Seba-san/ORR/processing/reportes/perfil_error_temporal_audio_01_10bd.png

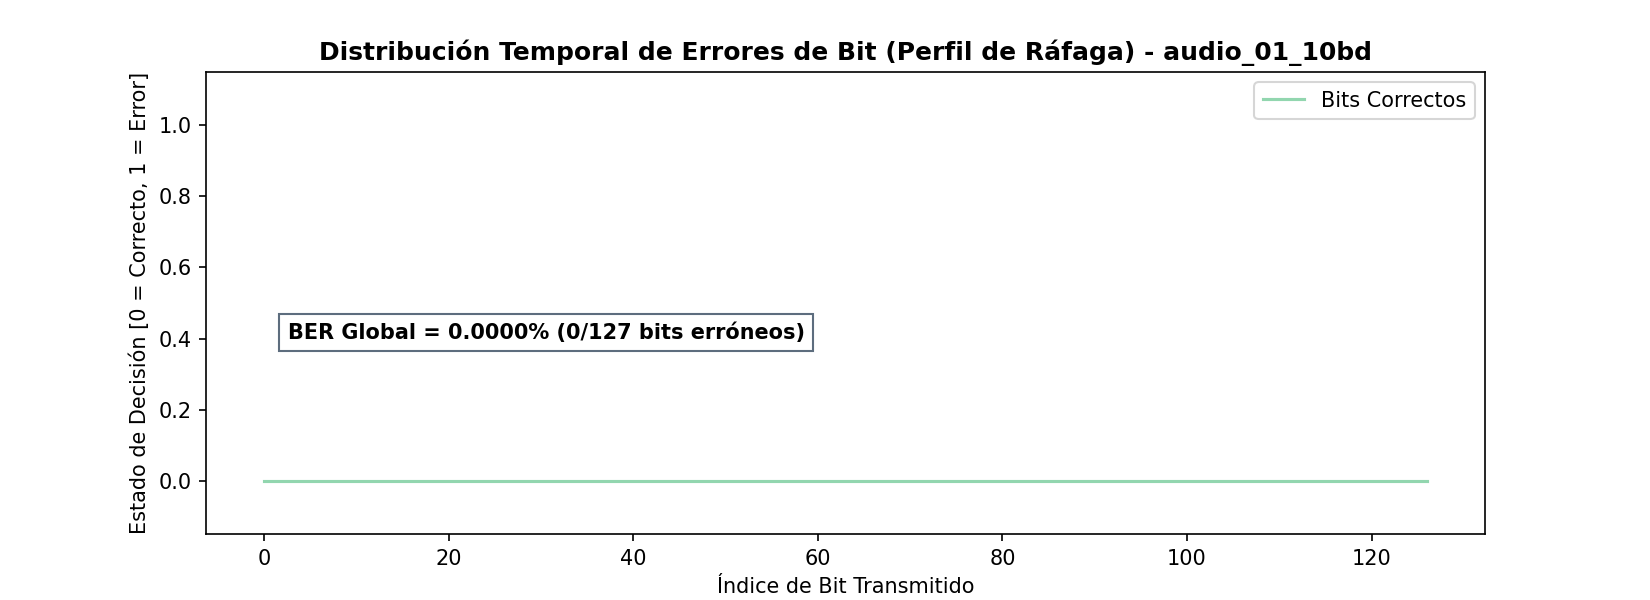
processing/reportes/perfil_error_temporal_audio_01_10bd.png
