Seba-san/ORR/firmware/rx/config.py

# --- CONFIGURACIONES GLOBALES ---
SAMPLE_RATE = 19200
BUFFER_SAMPLES = 19200  # 19200 muestras por bloque (1 segundo) para streaming
MAX_RECORD_SECONDS = 9999  # Límite superior indefinido para streaming
WIFI_SSID = 'PicoSDR'
WIFI_PASS = 'sdrpassword'
WIFI_IP = '192.168.4.1'
WEB_PORT = 80
ADC_PIN = 26  # GP26 es el Pin físico 31 (ADC0)
